wbledzinski/Battery_4_microInv/HW/R1/20220616-192426.jpg

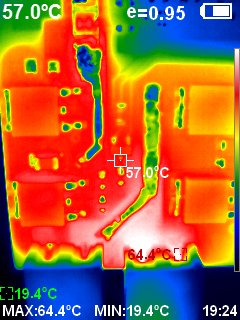
HW/R1/20220616-192426.jpg
